muumikan/EcumasterSerialDashboard/include/alarms_screen.hpp

#pragma once

#include <lvgl.h>

#include "dash_page.hpp"

namespace ecu {

// Everything that tripped this run, newest first, with the time it happened.
//
// The list the Diag page's "latched" block could never be: that one keeps a
// single slot per alarm type, so a coolant warning at 14:33 and another at
// 14:41 are one line. Here they are two, in the order they happened.
//
// There is no acknowledge button. This is a log the driver reads, not a queue
// an operator works through - in a car nobody is standing by to take
// responsibility for a row, and a button that only dims text is a button that
// takes attention away from the road.
class AlarmsScreen : public DashPage {
public:
    void create(lv_obj_t* parent) override;
    void update(const EngineDataModel& model,
                const AlarmEngine& alarms,
                const RunPeaks& peaks,
                uint32_t nowMs) override;

    const char* name() const override { return "ALARMS"; }

    // Up and down scroll the list when it is longer than the screen. Left and
    // right are left alone, so turning the page still works from here.
    bool onSwipe(lv_dir_t direction) override;

private:
    static constexpr uint8_t kVisibleRows = 11;

    // Scroll a screen at a time, keeping one row of overlap so the eye has
    // something to land on. The log holds 32 events, so this is three swipes
    // end to end at worst.
    static constexpr uint8_t kScrollStep = kVisibleRows - 1;

    struct Row {
        lv_obj_t* root = nullptr;
        lv_obj_t* stripe = nullptr;
        lv_obj_t* time = nullptr;
        lv_obj_t* label = nullptr;
        lv_obj_t* value = nullptr;
        lv_obj_t* rpm = nullptr;
        lv_obj_t* duration = nullptr;
        lv_obj_t* state = nullptr;
    };

    void buildHeader();
    void buildRows();
    void buildFooter();
    void paint(const AlarmEngine& alarms, uint32_t nowMs);

    Row rows_[kVisibleRows];

    lv_obj_t* empty_ = nullptr;
    lv_obj_t* activeCount_ = nullptr;
    lv_obj_t* totalCount_ = nullptr;
    lv_obj_t* runTime_ = nullptr;
    lv_obj_t* range_ = nullptr;
    lv_obj_t* since_ = nullptr;

    // Index of the topmost event on screen. Reset to 0 when a new event
    // arrives: the newest is at the top, and it is the one worth reading.
    uint8_t scrollTop_ = 0;
    uint8_t lastCount_ = 0;

    uint32_t lastRevision_ = UINT32_MAX;
    uint32_t lastPaintMs_ = 0;
    bool dirty_ = false;
};

}  // namespace ecu
