muumikan/EcumasterSerialDashboard/include/dash_theme.hpp

#pragma once

#include <lvgl.h>

// The dashboard's fixed palette. The screen is read in a dark cockpit, so
// there is one theme only - these values are the design, not a default.
namespace theme {

// Panels sit darker than the first pass and the dividing lines a little
// brighter. On the car the mid-grey cells washed out the numerals; the reading
// now comes from the digits against black, and the tiles are separated by
// their edges rather than by their fill.
//
// Every grey here is a true grey, R = G = B. The darkening pass before this
// one left them at values like 0x0D1113, where green and blue sit above red by
// a few counts. On paper that is a neutral so close to black it should not be
// visible; on the panel in the car it read as a green cast across every value
// tile. The IPS is not neutral enough to be trusted with a tint nobody asked
// for, so the tint is gone. Where a grey replaced a tinted one it keeps the
// same luminance, so nothing changes but the hue.
//
// The warning and critical fills below are deliberately coloured and stay.
inline lv_color_t bg()        { return lv_color_hex(0x000000); }
inline lv_color_t statusBg()  { return lv_color_hex(0x0A0A0A); }
inline lv_color_t panel()     { return lv_color_hex(0x000000); }
inline lv_color_t line()      { return lv_color_hex(0x343434); }
inline lv_color_t track()     { return lv_color_hex(0x161616); }
inline lv_color_t text()      { return lv_color_hex(0xF0F0F0); }
inline lv_color_t dim()       { return lv_color_hex(0x828282); }
inline lv_color_t dotOff()    { return lv_color_hex(0x383838); }

// What a measurement is called, on every cell that holds one. Yellow rather
// than the grey it started as: grey on black is the lowest contrast on the
// screen, it was the hardest thing to read in daylight, and yellow-on-black
// is what an Ecumaster dash looks like, so the panel now matches the software
// beside it.
//
// Deliberately clear of warn() below, which is an amber with red in it. These
// two are never far apart on screen and they must not be mistaken for each
// other: one is a name, the other is a verdict.
inline lv_color_t caption()   { return lv_color_hex(0xE8C547); }

inline lv_color_t good()      { return lv_color_hex(0x57C08A); }
inline lv_color_t warn()      { return lv_color_hex(0xE8A33D); }
inline lv_color_t crit()      { return lv_color_hex(0xE2504A); }
inline lv_color_t cyan()      { return lv_color_hex(0x58C7D6); }

// Tile backgrounds when a value goes out of range.
inline lv_color_t warnBg()    { return lv_color_hex(0x271E0D); }
inline lv_color_t warnEdge()  { return lv_color_hex(0x4A3A17); }
inline lv_color_t warnLabel() { return lv_color_hex(0xC0913F); }
inline lv_color_t critBg()    { return lv_color_hex(0x3E100D); }
inline lv_color_t critEdge()  { return lv_color_hex(0x7A2320); }
inline lv_color_t critLabel() { return lv_color_hex(0xE9A9A5); }
inline lv_color_t critValue() { return lv_color_hex(0xFFECEA); }

// Screen geometry, fixed by the panel.
constexpr lv_coord_t kShiftHeight = 6;
constexpr lv_coord_t kStatusHeight = 28;
constexpr lv_coord_t kChromeHeight = kShiftHeight + kStatusHeight;  // 34
constexpr lv_coord_t kPageWidth = 480;
constexpr lv_coord_t kPageHeight = 286;

}  // namespace theme
