muumikan/EcumasterSerialDashboard/include/engine_data_model.hpp

#pragma once

#include <stdint.h>

#include "engine_data.hpp"

namespace ecu {

// No fresh data for this long -> values are shown, but flagged as stale.
constexpr uint32_t kLinkStaleTimeoutMs = 500;

// No fresh data for this long -> the link is considered dead.
constexpr uint32_t kLinkOfflineTimeoutMs = 3000;

// Single source of truth for the UI.
//
// Holds the latest snapshot plus link health, and knows nothing about UART,
// framing or the EMU protocol. The UI only ever reads from here.
class EngineDataModel {
public:
    // Called by the provider whenever a decode pass produced data.
    void applySnapshot(const EngineSnapshot& snapshot, uint32_t nowMs);

    const EngineSnapshot& snapshot() const { return snapshot_; }

    LinkState linkState(uint32_t nowMs) const;

    // Milliseconds since the last accepted update. UINT32_MAX before the
    // first one.
    uint32_t ageMs(uint32_t nowMs) const;

    // Bumped only when at least one value actually changed, so the UI can
    // skip redraws cheaply.
    uint32_t revision() const { return revision_; }

    // Total number of accepted updates, for diagnostics.
    uint32_t updateCount() const { return updates_; }

    // Frames the link threw away. Zero on the classic protocol, which cannot
    // detect them; on EDL-1 a rising count means bytes are being lost upstream.
    void noteBadFrames(uint32_t total) { badFrames_ = total; }
    uint32_t badFrames() const { return badFrames_; }

private:
    EngineSnapshot snapshot_{};
    uint32_t lastUpdateMs_ = 0;
    uint32_t revision_ = 0;
    uint32_t updates_ = 0;
    uint32_t badFrames_ = 0;
    bool everUpdated_ = false;
};

// Is the engine stopped, as far as this dashboard can tell?
//
// Not the same question as `rpm < kEngineRunningRpm`, and the difference is
// the whole reason this exists. Killing the ignition cuts the ECU's power, so
// the last frame it ever sent freezes in the snapshot at whatever the engine
// was doing - often several hundred rpm, sometimes more. Read on its own, the
// rpm field then says "running" for as long as the dashboard stays powered.
//
// A dead link means the engine is stopped: it cannot be turning and reporting
// nothing. Anything the answer gates - the access point, and every write the
// service page accepts - has to ask it this way.
bool engineStopped(const EngineDataModel& model, uint32_t nowMs);

}  // namespace ecu
